JunKimmmy/USBPowerMeter/Firmware/ST/generate_frames.py

#!/usr/bin/env python3
"""
generate_frames.py — Convert dancing-banana GIF PROGMEM bitmaps to
STM32 SSD1315 OLED page-format C arrays.

Usage
-----
1. Paste the byte content of each epd_bitmap_frame_N_delay_0 array into
   the FRAME_RAW dict below (the hex bytes inside the braces).
2. Run:  python generate_frames.py
3. The script overwrites  Core/Src/banana_frames.c  in this project.
4. Rebuild the STM32 project — the OLED will show the real GIF frames.

Source format:  249 x 246 px, 1-bpp, MSB-first, 32 bytes per row.
                Bit = 1 → white/background,  bit = 0 → dark/figure.
Target format:  128 x 64 px, SSD1315 page-mode.
                fb[page][col]: bit n = row (page*8 + n), lit when set.
"""

import re, os, textwrap

SRC_W, SRC_H     = 249, 246
SRC_ROW_BYTES    = 32          # ceil(249/8) with 7 padding bits at end
OUT_W, OUT_H     = 128, 64
OUT_PAGES        = OUT_H // 8  # 8

# ──────────────────────────────────────────────────────────────────
# PASTE YOUR FRAME BYTES BELOW
# Copy everything between the outer braces of each PROGMEM array.
# Example:
#   0xff, 0xff, 0x00, ...
# ──────────────────────────────────────────────────────────────────
FRAME_RAW = {
    0: """
const unsigned char epd_bitmap_frame_0_delay_0 [] PROGMEM = {
	0xff, 0xff, 0xff, 0xff, 0xff, 0xff, 0xff, 0xff, 0xff, 0xff, 0xff, 0xff, 0xff, 0xff, 0xff, 0xff, 
	0xff, 0xff, 0xff, 0xff, 0xff, 0xff, 0xff, 0xff, 0xff, 0xff, 0xff, 0xff, 0xff, 0xff, 0xff, 0x80, 
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
	0xff, 0xff, 0xff, 0xff, 0xff, 0xff, 0xff, 0xff, 0xff, 0xff, 0xff, 0xff, 0xff, 0xff, 0xff, 0xff, 
	0xff, 0xff, 0xff, 0xff, 0xff, 0xff, 0xff, 0xff, 0xff, 0xff, 0xff, 0xff, 0xff, 0xff, 0xff, 0x80, 
	0xff, 0xff, 0xff, 0xff, 0xff, 0xff, 0xff, 0xff, 0xff, 0xff, 0xff, 0xff, 0xff, 0xff, 0xff, 0xff, 
	0xff, 0xff, 0xff, 0xff, 0xff, 0xff, 0xff, 0xff, 0xff, 0xff, 0xff, 0xff, 0xff, 0xff, 0xff, 0x80, 
	0xff, 0xff, 0xff, 0xff, 0xff, 0xff, 0xff, 0xff, 0xff, 0xff, 0xff, 0xff, 0xff, 0xff, 0xff, 0xff, 
	0xff, 0xff, 0xff, 0xff, 0xff, 0xff, 0xff, 0xff, 0xff, 0xff, 0xff, 0xff, 0xff, 0xff, 0xff, 0x80, 
	0xff, 0xff, 0xff, 0xff, 0xff, 0xff, 0xff, 0xff, 0xff, 0xff, 0xff, 0xff, 0xff, 0xff, 0xff, 0xff, 
	0xff, 0xff, 0xff, 0xff, 0xff, 0xff, 0xff, 0xff, 0xff, 0xff, 0xff, 0xff, 0xff, 0xff, 0xff, 0x80, 
	0xff, 0xff, 0xff, 0xff, 0xff, 0xff, 0xff, 0xff, 0xff, 0xff, 0xff, 0xff, 0xff, 0xff, 0xff, 0xff, 
	0xff, 0xff, 0xff, 0xff, 0xff, 0xff, 0xff, 0xff, 0xff, 0xff, 0xff, 0xff, 0xff, 0xff, 0xff, 0x80, 
	0xff, 0xff, 0xff, 0xff, 0xff, 0xff, 0xff, 0xff, 0xff, 0xff, 0xff, 0xff, 0xff, 0xff, 0xff, 0xff, 
	0xff, 0xff, 0xff, 0xff, 0xff, 0xff, 0xff, 0xff, 0xff, 0xff, 0xff, 0xff, 0xff, 0xff, 0xff, 0x80, 
	0xff, 0xff, 0xff, 0xff, 0xff, 0xff, 0xff, 0xff, 0xff, 0xff, 0xff, 0xff, 0xff, 0xff, 0xff, 0xff, 
	0xff, 0xff, 0xff, 0xff, 0xff, 0xff, 0xff, 0xff, 0xff, 0xff, 0xff, 0xff, 0xff, 0xff, 0xff, 0x80, 
	0xff, 0xff, 0xff, 0xff, 0xff, 0xff, 0xff, 0xff, 0xff, 0xff, 0xff, 0xff, 0xff, 0xff, 0xff, 0xff, 
	0xff, 0xff, 0xff, 0xff, 0xff, 0xff, 0xff, 0xff, 0xff, 0xff, 0xff, 0xff, 0xff, 0xff, 0xff, 0x80, 
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
};

// Array of all bitmaps for convenience. (Total bytes used to store images in PROGMEM = 7888)
const int epd_bitmap_allArray_LEN = 1;
const unsigned char* epd_bitmap_allArray[1] = {
	epd_bitmap_frame_0_delay_0
};
    """,
    4: """
    /* paste frame 4 bytes here */
    """,
    5: """
    /* paste frame 5 bytes here */
    """,
    6: """
    /* paste frame 6 bytes here */
    """,
    7: """
    /* paste frame 7 bytes here */
    """,
}
# ──────────────────────────────────────────────────────────────────


def parse_bytes(raw: str) -> bytes:
    """Extract all 0xNN hex bytes from a C array literal string."""
    return bytes(int(x, 16) for x in re.findall(r'0x([0-9a-fA-F]{2})', raw))


def get_pixel(data: bytes, x: int, y: int) -> int:
    """Return 1 (white/off) or 0 (dark/on) for source pixel (x, y)."""
    idx = y * SRC_ROW_BYTES + x // 8
    if idx >= len(data):
        return 1  # treat out-of-bounds as white background
    return (data[idx] >> (7 - x % 8)) & 1


def scale_frame(data: bytes):
    """
    Nearest-neighbour downscale 249x246 → 128x64.
    Returns pages[8][128] in SSD1315 page-mode format.
    Source 0 (dark) maps to OLED bit set (pixel lit).
    Source 1 (white) maps to OLED bit clear (pixel off).
    """
    pages = [[0] * OUT_W for _ in range(OUT_PAGES)]
    for oy in range(OUT_H):
        sy = oy * SRC_H // OUT_H
        for ox in range(OUT_W):
            sx = ox * SRC_W // OUT_W
            if get_pixel(data, sx, sy) == 0:   # dark pixel → ON
                pages[oy // 8][ox] |= 1 << (oy % 8)
    return pages


def main():
    script_dir = os.path.dirname(os.path.abspath(__file__))
    out_path   = os.path.join(script_dir, 'Core', 'Src', 'banana_frames.c')

    scaled = []
    for fi in sorted(FRAME_RAW):
        raw  = FRAME_RAW[fi]
        data = parse_bytes(raw)
        expected = SRC_ROW_BYTES * SRC_H
        if len(data) < expected:
            print(f'WARNING: frame {fi} has {len(data)} bytes, expected {expected}.'
                  f'  Did you paste the full array?')
        scaled.append(scale_frame(data))
        print(f'Processed frame {fi}  ({len(data)} bytes)')

    with open(out_path, 'w') as f:
        f.write('#include "banana_frames.h"\n\n')
        f.write('/* Auto-generated by generate_frames.py — do not hand-edit. */\n\n')
        f.write('const uint8_t BANANA_FRAMES_READY = 1;\n\n')
        f.write('const uint8_t banana_frames'
                '[BANANA_FRAME_COUNT][BANANA_FRAME_PAGES][BANANA_FRAME_COLS] = {\n')
        for fi, pages in enumerate(scaled):
            f.write(f'    /* frame {fi} */\n    {{\n')
            for pi, row in enumerate(pages):
                hex_vals = ', '.join(f'0x{b:02x}' for b in row)
                f.write(f'        /* page {pi} */ {{ {hex_vals} }},\n')
            f.write('    },\n')
        f.write('};\n')

    n = len(scaled)
    total_bytes = n * OUT_PAGES * OUT_W
    print(f'\nWrote {out_path}')
    print(f'{n} frames  x  {OUT_PAGES} pages  x  {OUT_W} cols  =  {total_bytes} bytes flash')
    print('Rebuild the STM32 project to use the real GIF frames.')


if __name__ == '__main__':
    main()
